Valsvirtuals/ZipLine/STL/finger guide/zip guide 10.stl

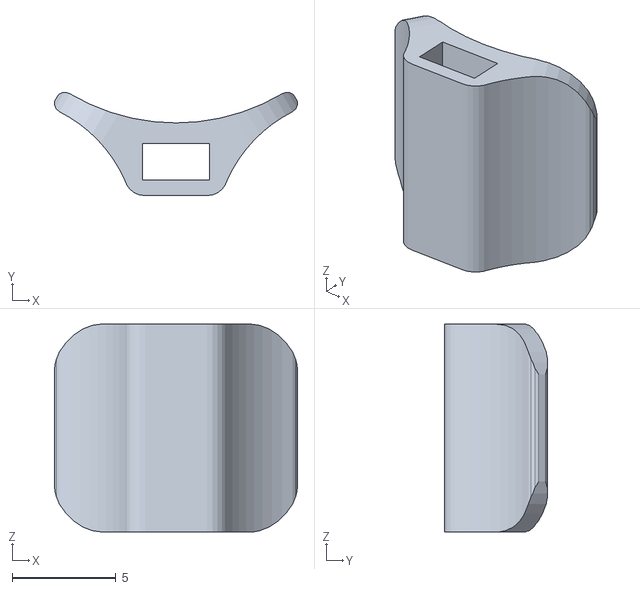
[picture p20: CAD file, 2022-01-24]
STL/finger guide/zip guide 10.stl
11.7 x 4.97 x 10.0
