Valsvirtuals/ZipLine/STL/finger tracking module (FTM)/z24 gear.stl

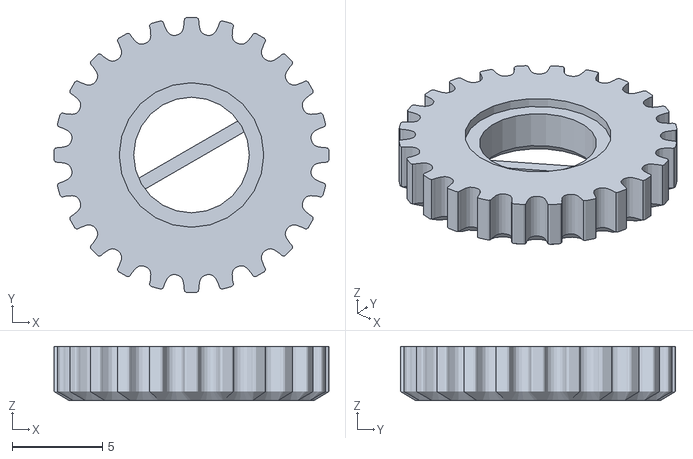
[picture p21: CAD file, 2022-01-24]
STL/finger tracking module (FTM)/z24 gear.stl
15.2 x 15.2 x 3.00
