Valsvirtuals/ZipLine/STL/finger guide/zip tip 15.stl

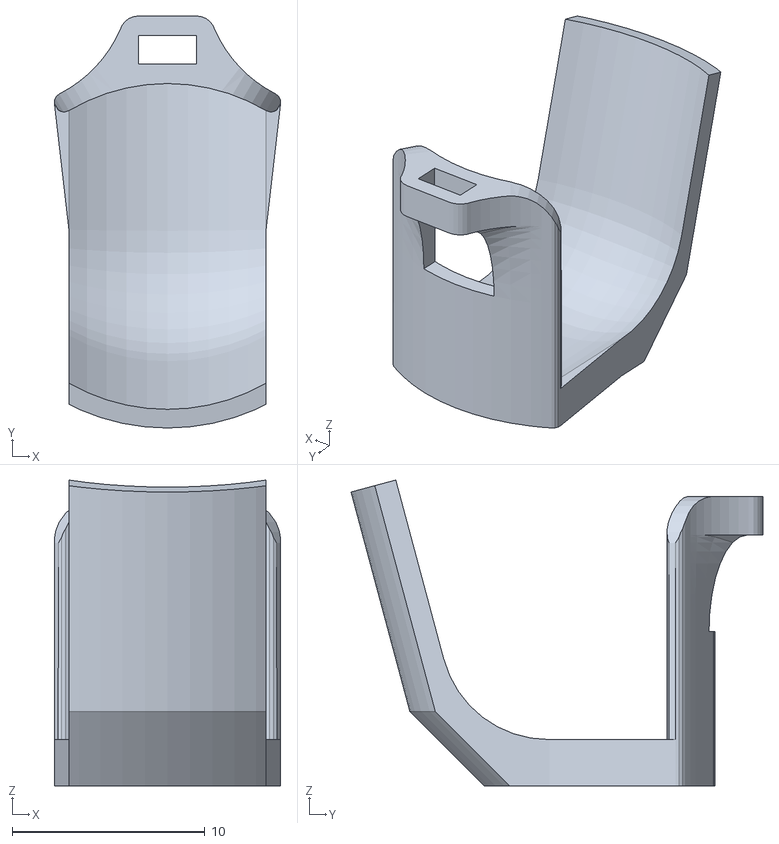
[picture p22: CAD file, 2022-01-24]
STL/finger guide/zip tip 15.stl
11.7 x 21.3 x 15.9
