Valsvirtuals/ZipLine/STL/finger tracking module (FTM)/frame.stl

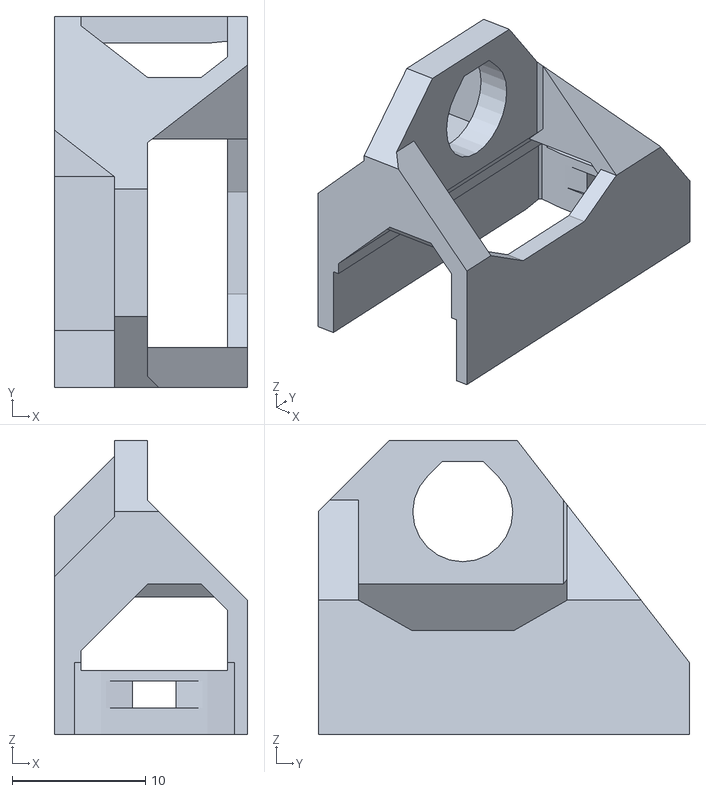
[picture p23: CAD file, 2022-01-24]
STL/finger tracking module (FTM)/frame.stl
14.5 x 27.8 x 22.1
