Valsvirtuals/ZipLine/STL/finger guide/zip guide 20.stl

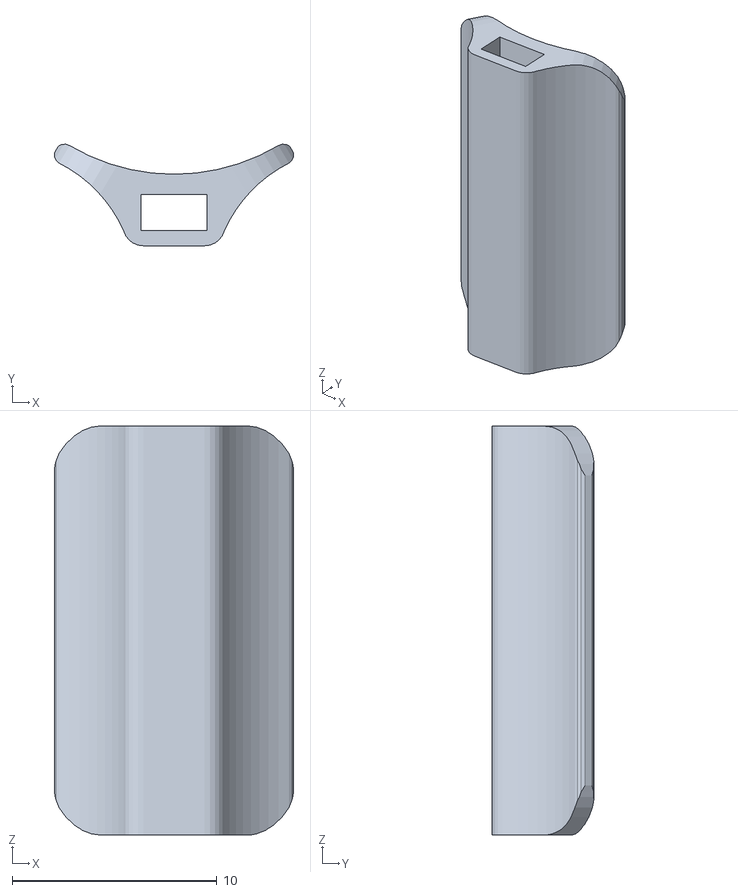
[picture p24: CAD file, 2022-01-24]
STL/finger guide/zip guide 20.stl
11.7 x 4.97 x 20.0
