Valsvirtuals/ZipLine/STL/finger guide/zip guide 30.stl

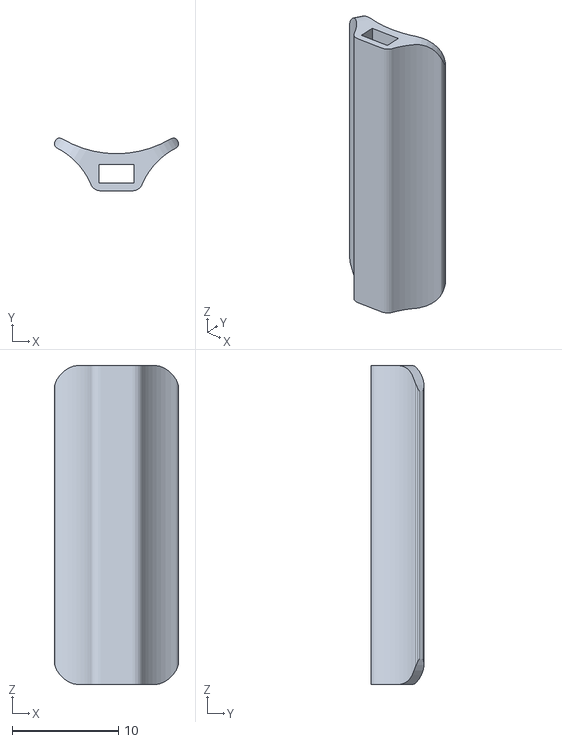
[picture p25: CAD file, 2022-01-24]
STL/finger guide/zip guide 30.stl
11.7 x 4.97 x 30.0
