Valsvirtuals/ZipLine/STL/finger guide/zip guide 25.stl

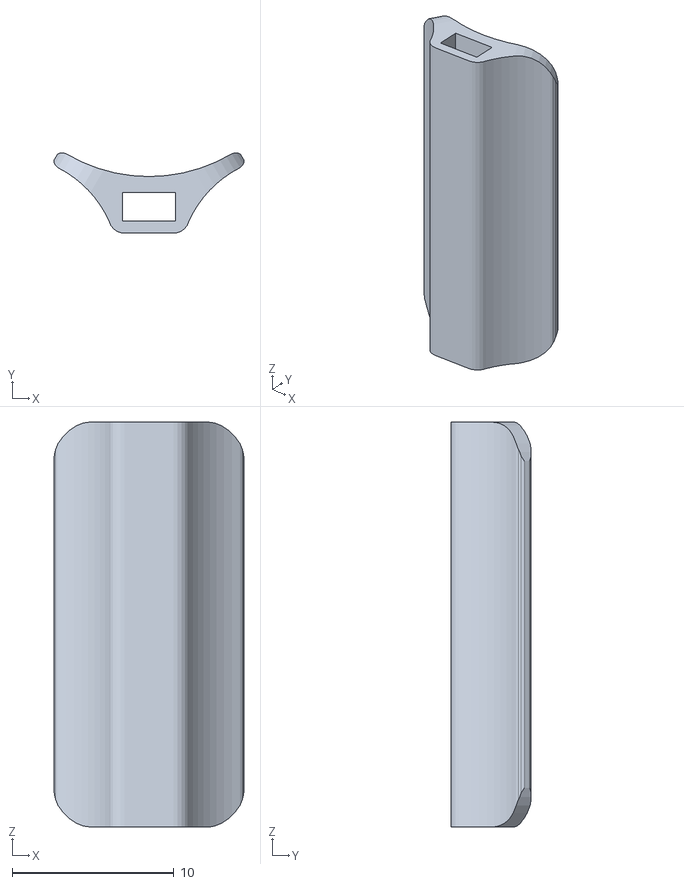
[picture p26: CAD file, 2022-01-24]
STL/finger guide/zip guide 25.stl
11.7 x 4.97 x 25.0
