Valsvirtuals/ZipLine/STL/finger guide/zip tip 25.stl

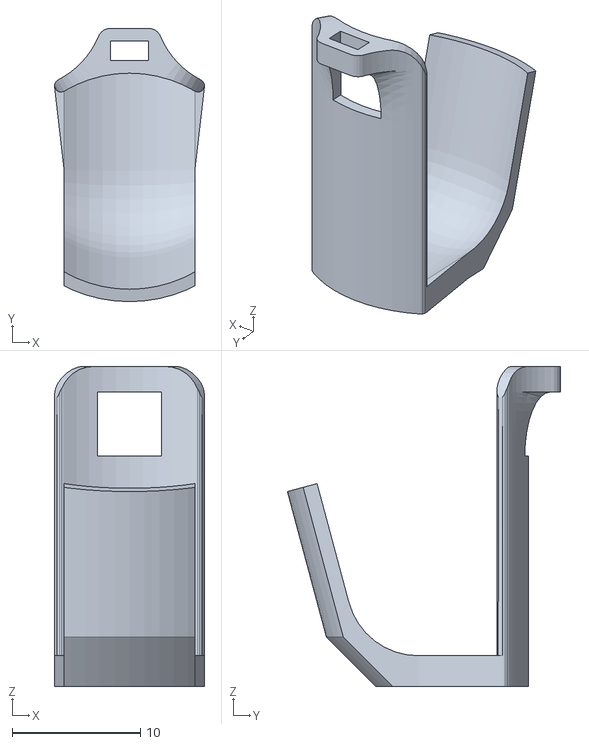
[picture p27: CAD file, 2022-01-24]
STL/finger guide/zip tip 25.stl
11.7 x 21.3 x 25.0
