Valsvirtuals/ZipLine/STL/finger guide/zip tip 10.stl

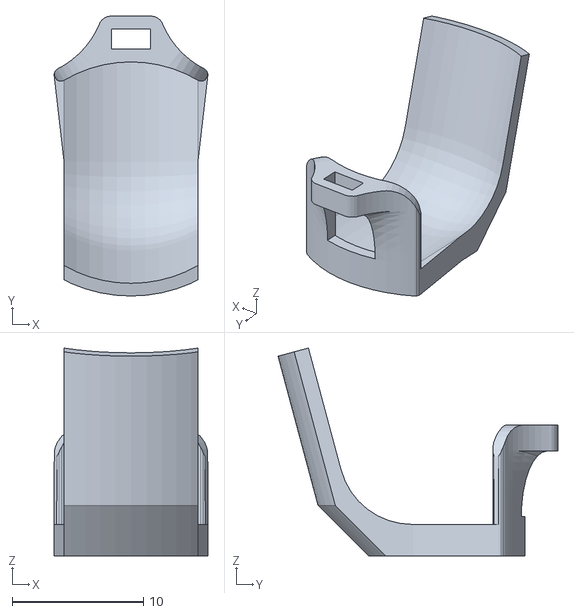
[picture p28: CAD file, 2022-01-24]
STL/finger guide/zip tip 10.stl
11.7 x 21.3 x 15.9
