Valsvirtuals/ZipLine/STL/finger guide/zip guide 40.stl

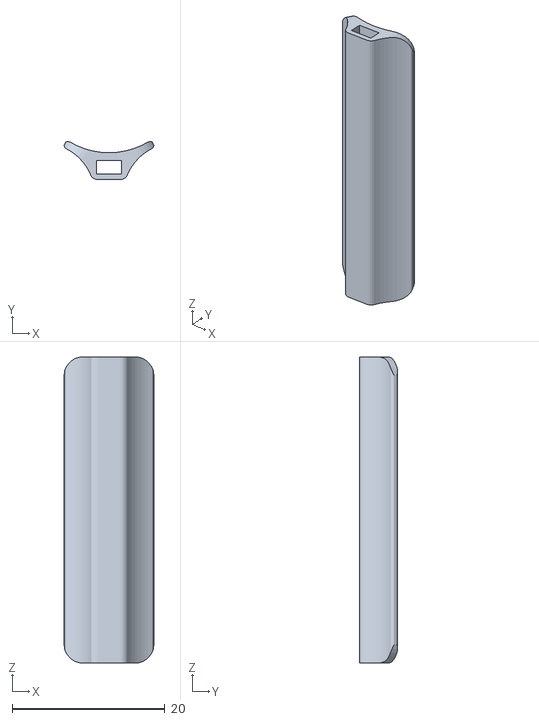
[picture p29: CAD file, 2022-01-24]
STL/finger guide/zip guide 40.stl
11.7 x 4.97 x 40.0
