Valsvirtuals/ZipLine/STL/finger guide/zip guide 15.stl

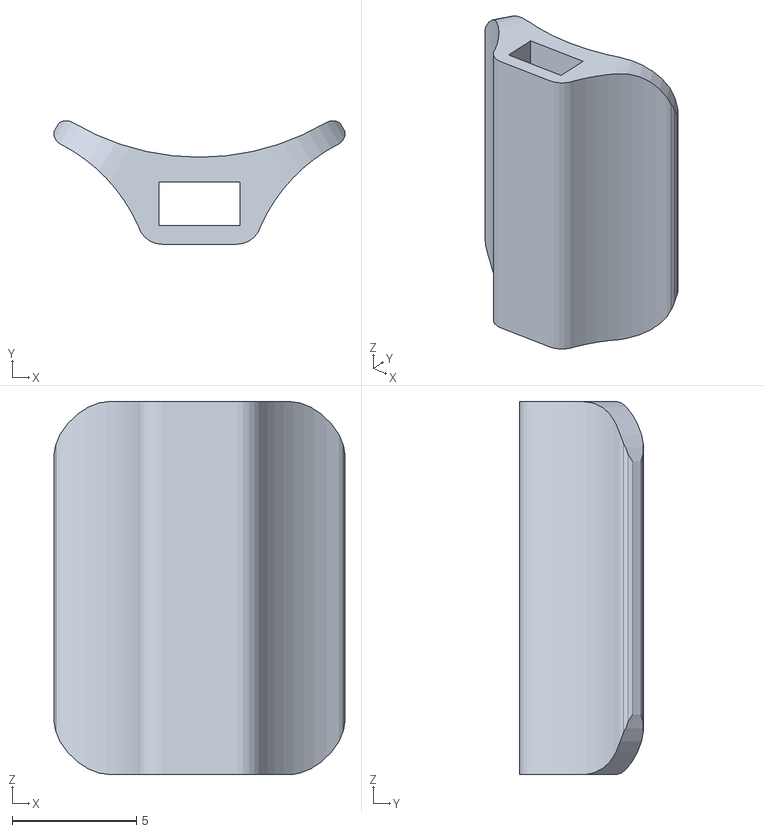
[picture p30: CAD file, 2022-01-24]
STL/finger guide/zip guide 15.stl
11.7 x 4.97 x 15.0
