Valsvirtuals/ZipLine/STL/finger guide/zip tip 30.stl

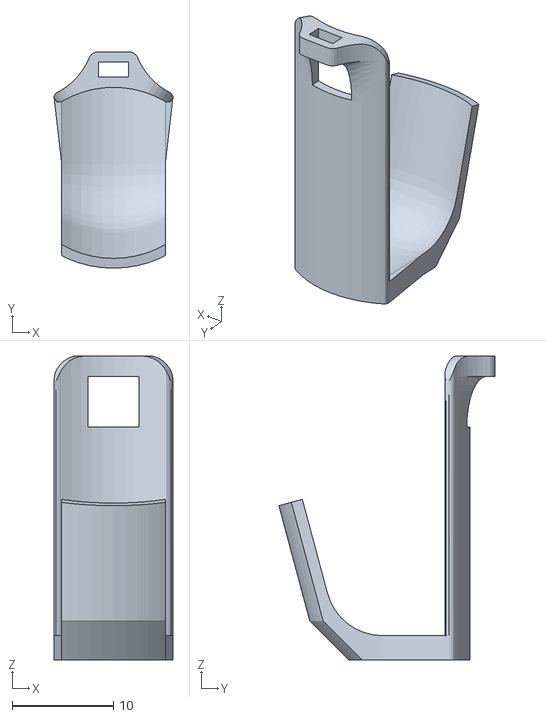
[picture p31: CAD file, 2022-01-24]
STL/finger guide/zip tip 30.stl
11.7 x 21.3 x 30.0
